carlosedp/PMOD1/Kicad-RingPush/V1.1/RingPush-PMOD.sch

## KiCad design Kicad-RingPush/V1.1/RingPush-PMOD.sch (2021-06-04)

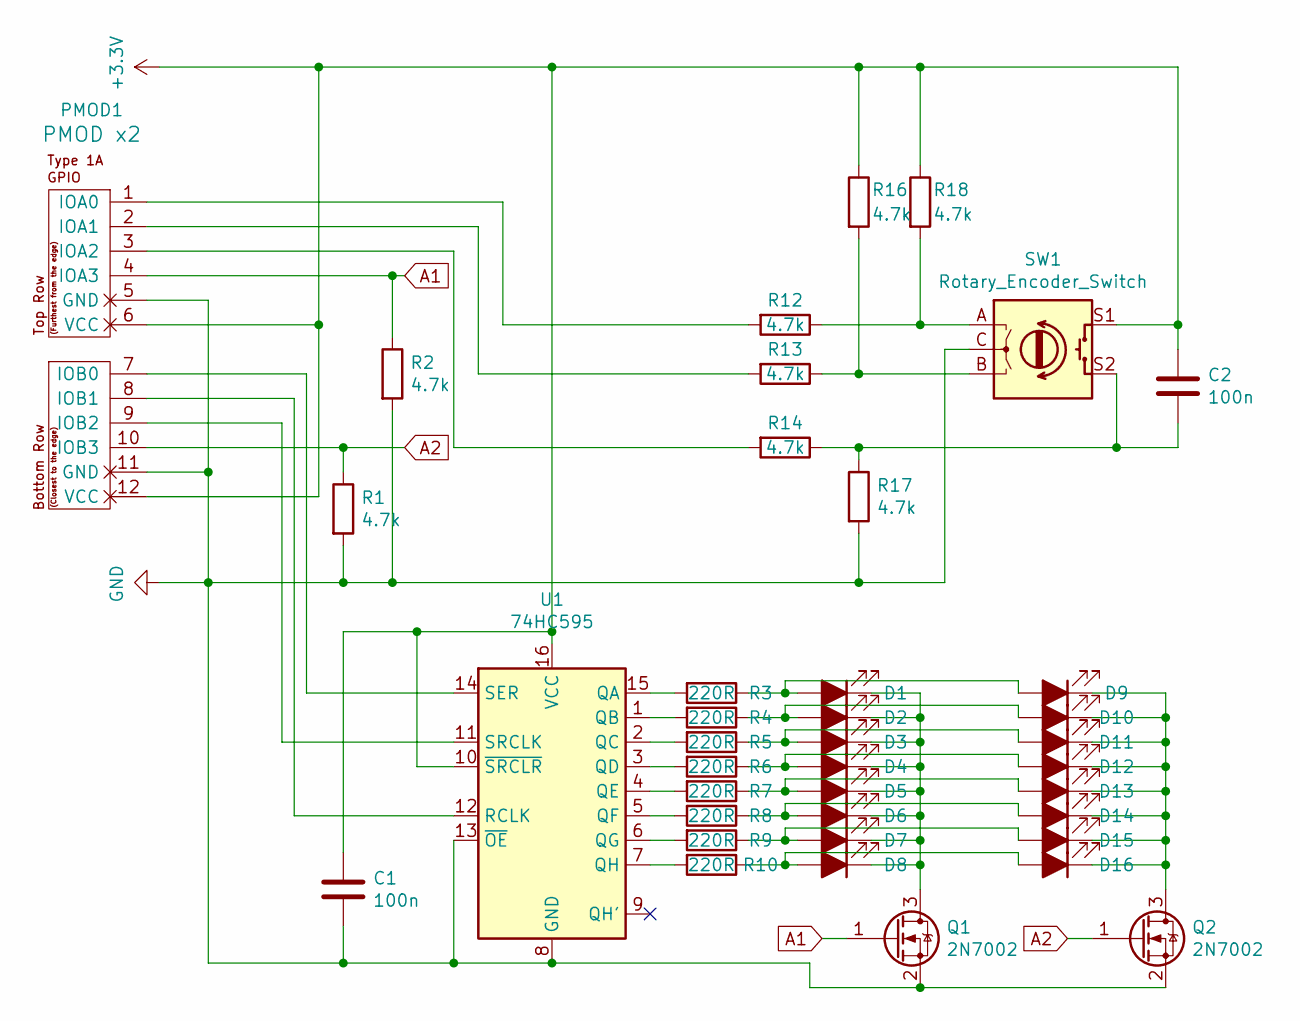
[picture p7: schematic RingPush-PMOD.sch]

Parts:
C1, C2: 100n; C_0603_1608Metric_Pad1.08x0.95mm_HandSolder
D1, D2, D3, D4, D5, D6, D7, D8, D9, D10, D11, D12, D13, D14, D15, D16: LED_ALT; LED_0805_2012Metric_Pad1.15x1.40mm_HandSolder
PMOD1: PMOD-Device-x2-Type-1A-GPIO; pmod_pin_array_6x2
Q1, Q2: 2N7002; SOT-23
R1, R2, R12, R13, R14, R16, R17, R18: 4.7k; R_0603_1608Metric_Pad0.98x0.95mm_HandSolder
R3, R4, R5, R6, R7, R8, R9, R10: 220R; R_0603_1608Metric_Pad0.98x0.95mm_HandSolder
SW1: Rotary_Encoder_Switch; RotaryEncoder_Alps_EC11E-Switch_Vertical_H20mm
U1: 74HC595; SOIC-16_3.9x9.9mm_P1.27mm

Connections:
+3.3V: C1.1, C2.1, PMOD1.6 (VCC), PMOD1.12 (VCC), R16.1, R18.1, SW1.S1, U1.10 (~SRCLR), U1.16 (VCC)
A1: PMOD1.4 (IOA3), Q1.1 (G), R2.1
A2: PMOD1.10 (IOB3), Q2.1 (G), R1.1
GND: C1.2, PMOD1.5 (GND), PMOD1.11 (GND), Q1.2 (S), Q2.2 (S), R1.2, R2.2, R17.2, SW1.C, U1.8 (GND), U1.13 (~OE)
unnamed: C2.2, R14.1, R17.1, SW1.S2
unnamed: D1.1 (K), D2.1 (K), D3.1 (K), D4.1 (K), D5.1 (K), D6.1 (K), D7.1 (K), D8.1 (K), Q1.3 (D)
unnamed: D1.2 (A), D9.2 (A), R3.1
unnamed: D9.1 (K), D10.1 (K), D11.1 (K), D12.1 (K), D13.1 (K), D14.1 (K), D15.1 (K), D16.1 (K), Q2.3 (D)
unnamed: D2.2 (A), D10.2 (A), R4.1
unnamed: D3.2 (A), D11.2 (A), R5.1
unnamed: D4.2 (A), D12.2 (A), R6.1
unnamed: D5.2 (A), D13.2 (A), R7.1
unnamed: D6.2 (A), D14.2 (A), R8.1
unnamed: D7.2 (A), D15.2 (A), R9.1
unnamed: D8.2 (A), D16.2 (A), R10.1
unnamed: PMOD1.1 (IOA0), R12.2
unnamed: PMOD1.2 (IOA1), R13.2
unnamed: PMOD1.3 (IOA2), R14.2
unnamed: PMOD1.7 (IOB0), U1.14 (SER)
unnamed: PMOD1.8 (IOB1), U1.12 (RCLK)
unnamed: PMOD1.9 (IOB2), U1.11 (SRCLK)
unnamed: R3.2, U1.15 (QA)
unnamed: R4.2, U1.1 (QB)
unnamed: R5.2, U1.2 (QC)
unnamed: R6.2, U1.3 (QD)
unnamed: R7.2, U1.4 (QE)
unnamed: R8.2, U1.5 (QF)
unnamed: R9.2, U1.6 (QG)
unnamed: R10.2, U1.7 (QH)
unnamed: R12.1, R18.2, SW1.A
unnamed: R13.1, R16.2, SW1.B
